Unified-Daughterboard/UDB-C-Legacy/Images/C2-Dimens.png

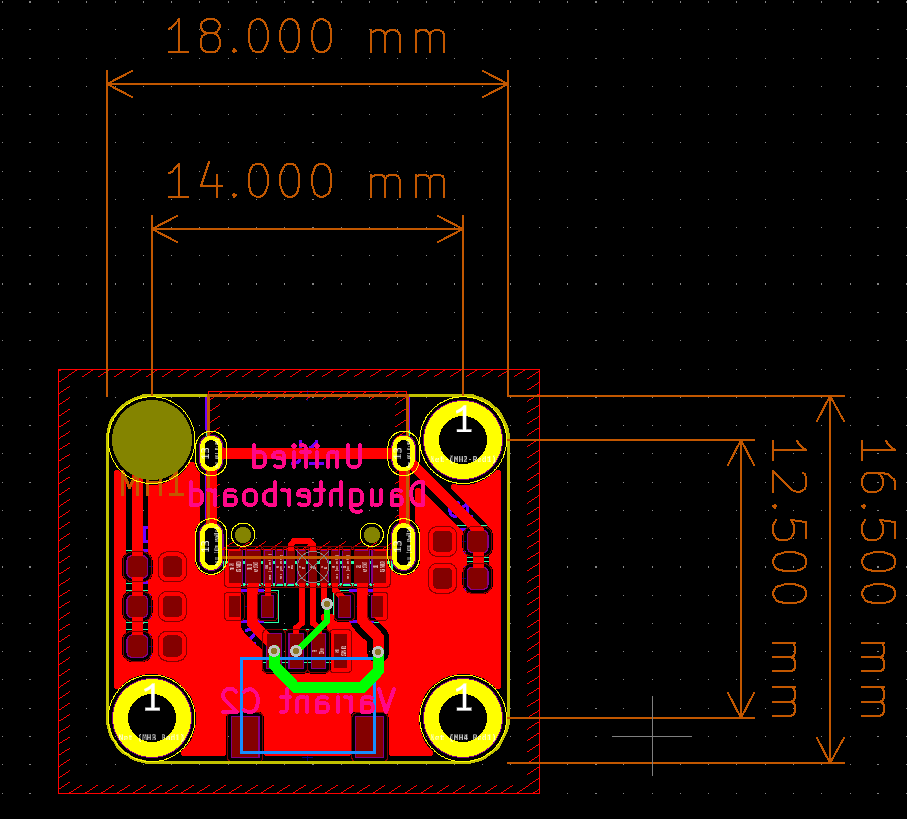
Images/C2-Dimens.png
