Unified-Daughterboard/UDB-C-Legacy/Images/Daughterboard-C2.png

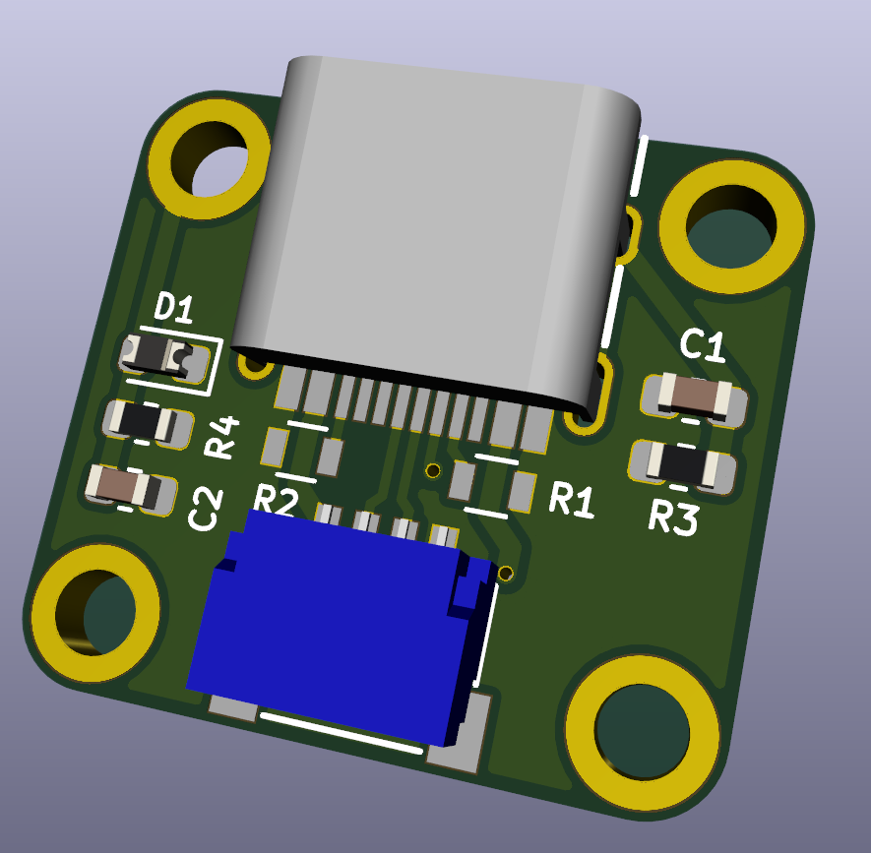
Images/Daughterboard-C2.png
