Unified-Daughterboard/UDB-C-Legacy/Images/jst-incorrect.png

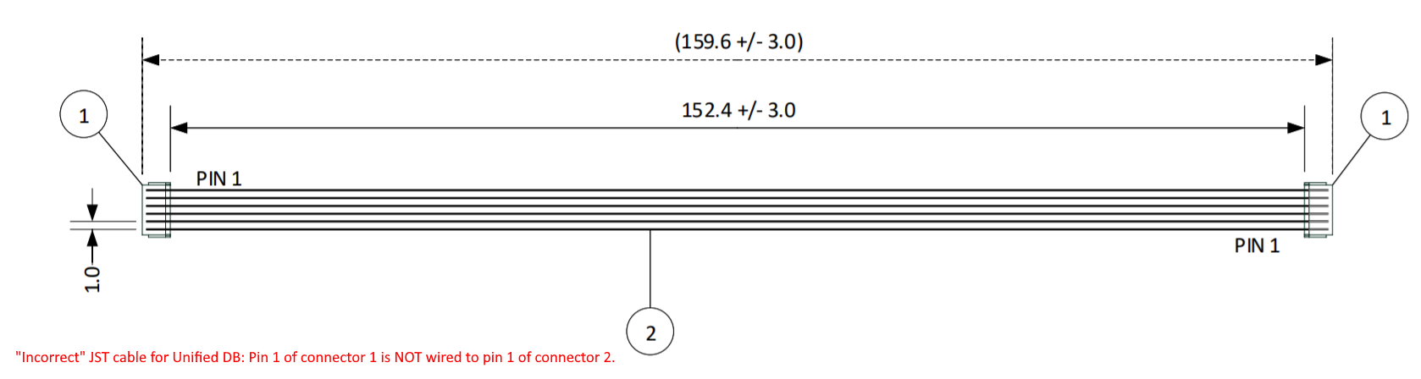
Images/jst-incorrect.png
