Unified-Daughterboard/UDB-C-Legacy/Images/repoCard.png

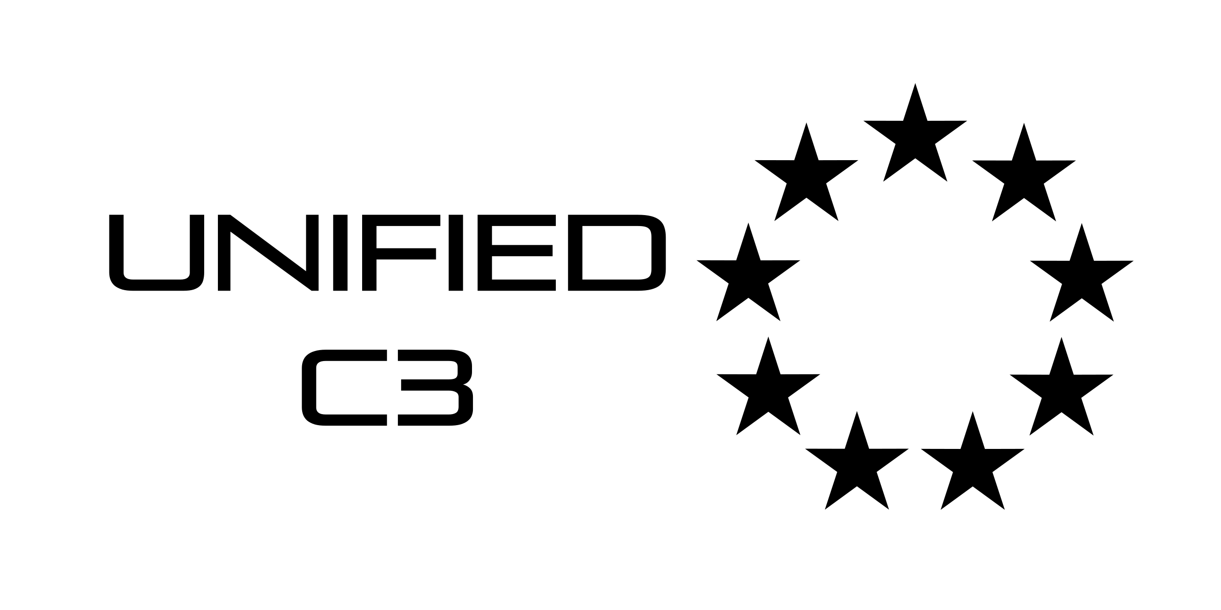
Images/repoCard.png
