Unified-Daughterboard/UDB-C-Legacy/Images/unifiedName.png

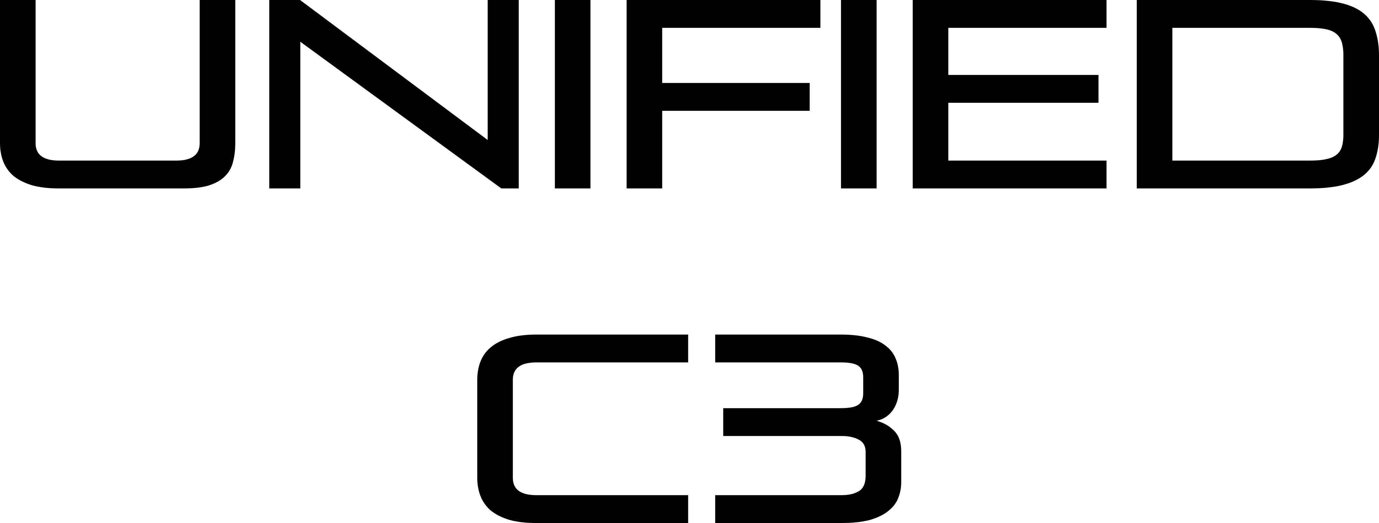
Images/unifiedName.png
